ian-rose/costco-tree-controller/KiCad/schematic.kicad_sch

## KiCad design KiCad/schematic.kicad_sch (2023-12-26)

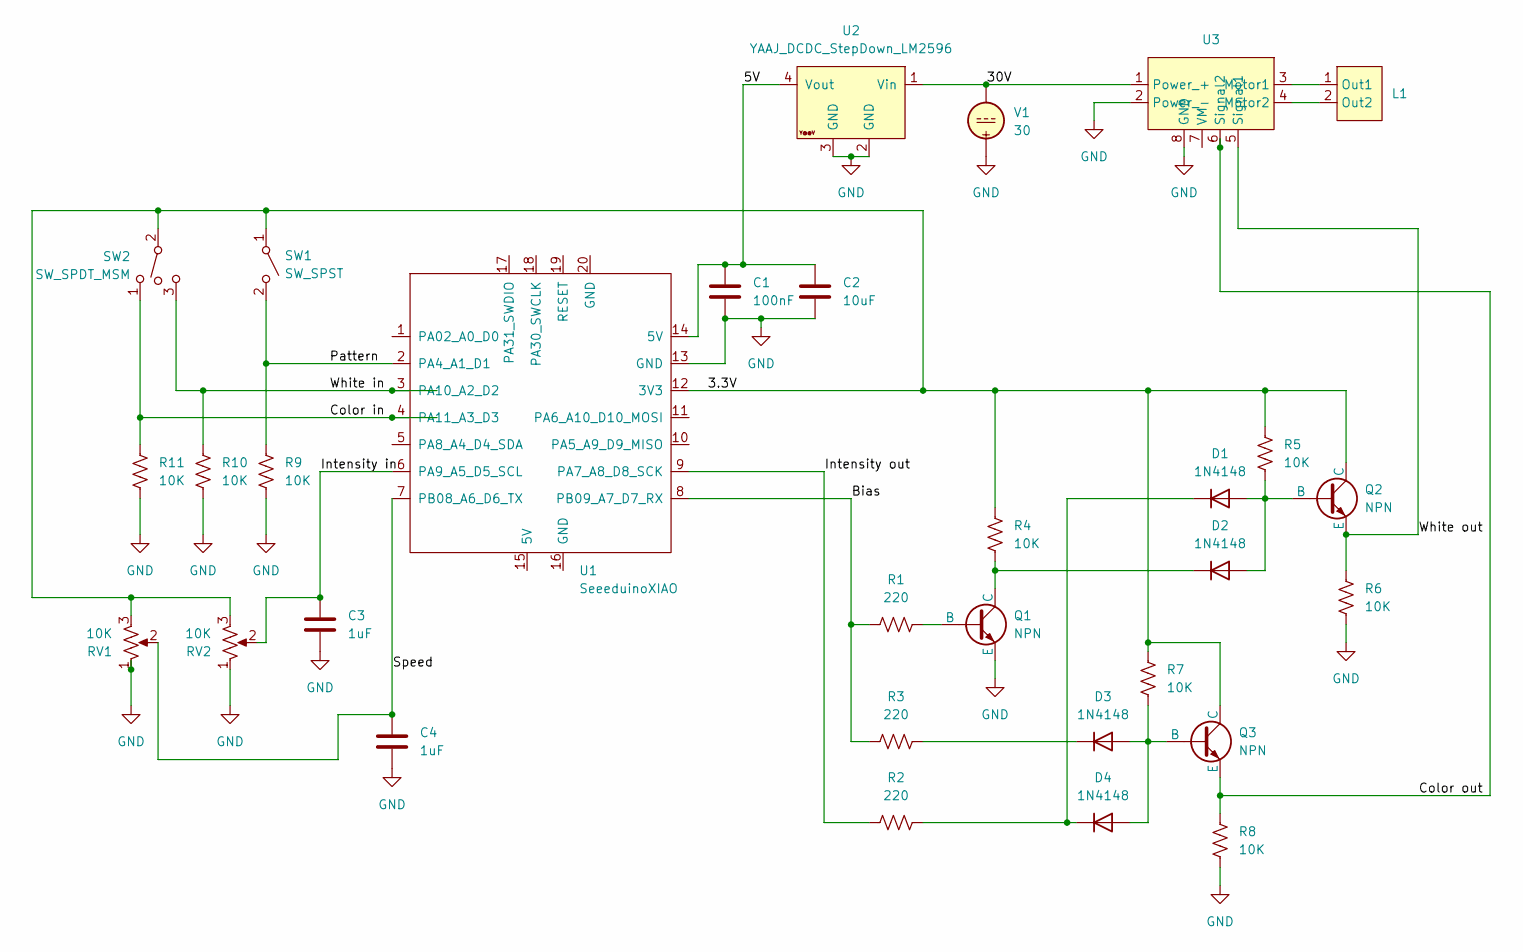
[picture p3: schematic schematic.kicad_sch]

Parts:
C1: 100nF; C_Disc_D5.0mm_W2.5mm_P5.00mm
C2: 10uF; C_Disc_D5.1mm_W3.2mm_P5.00mm
C3, C4: 1uF; C_Disc_D5.0mm_W2.5mm_P5.00mm
D1, D2, D3, D4: 1N4148; D_T-1_P5.08mm_Horizontal
L1: Terminal block
Q1, Q2, Q3: NPN; 2n3094
R1, R2, R3: 220; R_Axial_DIN0207_L6.3mm_D2.5mm_P7.62mm_Horizontal
R4, R5, R6, R7, R8, R9, R10, R11: 10K; R_Axial_DIN0207_L6.3mm_D2.5mm_P7.62mm_Horizontal
RV1, RV2: 10K; Adafruit Potentiometer
SW1: SW_SPST; 2P2T
SW2: SW_SPDT_MSM; 2P3T
U1: SeeeduinoXIAO; Seeeduino XIAO-MOUDLE14P-2.54-21X17.8MM
U2: YAAJ_DCDC_StepDown_LM2596
U3: Adafruit DRV8871
V1: 30; Terminal block

Connections:
3.3V: Q2.1 (C), Q3.1 (C), R4.2, R5.2, R7.2, RV1.3, RV2.3, SW1.1 (A), SW2.2, U1.12 (3V3)
5V: C1.1, C2.1, U1.14 (5V), U2.4 (Vout)
30V: U2.1 (Vin), U3.1 (Power_+), V1.2
Bias: R1.1, R3.1, U1.8 (PB09_A7_D7_RX)
Color in: R11.2, SW2.1, U1.4 (PA11_A3_D3)
Color out: Q3.3 (E), R8.2, U3.6 (Signal2)
GND: C1.2, C2.2, C3.1, C4.1, Q1.3 (E), R6.1, R8.1, R9.1, R10.1, R11.1, RV1.1, RV2.1, U1.13 (GND), U2.2 (GND), U2.3 (GND), U3.2 (Power_-), U3.8 (GND), V1.1
Intensity in: C3.2, RV2.2, U1.6 (PA9_A5_D5_SCL)
Intensity out: R2.1, U1.9 (PA7_A8_D8_SCK)
unnamed: D1.1 (K), D4.1 (K), R2.2
unnamed: D1.2 (A), D2.2 (A), Q2.2 (B), R5.1
unnamed: D2.1 (K), Q1.1 (C), R4.1
unnamed: D3.1 (K), R3.2
unnamed: D3.2 (A), D4.2 (A), Q3.2 (B), R7.1
unnamed: L1.1 (Out1), U3.3 (Motor1)
unnamed: L1.2 (Out2), U3.4 (Motor2)
unnamed: Q1.2 (B), R1.2
Pattern: R9.2, SW1.2 (B), U1.2 (PA4_A1_D1)
Speed: C4.2, RV1.2, U1.7 (PB08_A6_D6_TX)
White in: R10.2, SW2.3, U1.3 (PA10_A2_D2)
White out: Q2.3 (E), R6.2, U3.5 (Signal1)
